RogerParkinson/vortex-manipulator/src/Sleep.cpp

/*
 * Sleep.cpp
 *
 *  Created on: 28/04/2013
 *      Author: roger
 */

#include "Sleep.h"

static uint16_t myicon[] PROGMEM = {
	0x0000,0x0000,0x0000,0x0000,0x0000,0x0000,0x0000,0x0000,0x0000,0x0000,0x0000,0x0000,0x0000,0x0000,0x0000,0x0000,0x0000,0x0000,0x0000,0x0000,0x0000,0x0000,0x0000,0x0000,0x0000,0x0000,0x0000,0x0000,
	0x0000,0x0000,0x0000,0x0000,0x0000,0x0000,0x0000,0x0000,0x0000,0x0000,0x0000,0x0000,0x0000,0x0000,0x0000,0x0000,0x0000,0x0000,0x0000,0x0000,0x0000,0x0000,0x0000,0x0000,0x0000,0x0000,0x0000,0x0000,
	0x0000,0x0000,0x0000,0x0000,0x0000,0x0000,0x0000,0x0000,0x0000,0x0000,0x0000,0x0000,0x0000,0x0000,0x0000,0x0000,0x0000,0x0000,0x0000,0x0000,0x0000,0x0000,0x0000,0x0000,0x0000,0x0000,0x0000,0x0000,
	0x0000,0x0000,0x0000,0x0000,0x0000,0x0000,0x0000,0x0000,0x0000,0x0000,0x0000,0x39c7,0x3186,0x0000,0x0000,0x0000,0x0000,0x0000,0x0000,0x0000,0x0000,0x0000,0x0000,0x0000,0x0000,0x0000,0x0000,0x0000,
	0x0000,0x0000,0x0000,0x0000,0x0000,0x0000,0x0000,0x0000,0x0000,0x630c,0xe71c,0xd69a,0x0841,0x0000,0x0000,0x0000,0x0000,0x0000,0x0000,0x0000,0x0000,0x0000,0x0000,0x0000,0x0000,0x0000,0x0000,0x0000,
	0x0000,0x0000,0x0000,0x0000,0x0000,0x0000,0x0000,0x0000,0xce59,0xffdf,0xffdf,0x0841,0x0000,0x0000,0x0000,0x0000,0x0000,0x0000,0x0000,0x0000,0x0000,0x0000,0x0000,0x0000,0x0000,0x0000,0x0000,0x0000,
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

Sleep::Sleep(): App() {
	// Keep the constructor empty and do most things in the init()
}
void Sleep::init() {
	m_icon = new Icon(28,myicon);
}

void Sleep::setup() {
	Graphics.fillScreen(BLACK);
	Graphics.setRotation(3);
	m_buttonShutdown->draw();
//	m_buttonSleep->draw();
}

void Sleep::close() {
}

boolean Sleep::touch(TS_Point p) {
	if (m_buttonShutdown->isClicked(p)) {
		m_buttonShutdown->flash();
		Hardware.shutdown();

		Appregistry.jumpToMenu();
		Appregistry.getCurrentApp()->setup();
		Appregistry.getCurrentApp()->display();
	}
	if (m_buttonSleep->isClicked(p)) {
		m_buttonSleep->flash();
		Hardware.sleep();
	}
	return true;
}
void Sleep::display() {
}

Sleep::~Sleep() {
}

App *sleep = new Sleep();
