RogerParkinson/vortex-manipulator/src/ui/Startup.h

/*
 * Startup.h
 *
 *  Created on: Oct 14, 2018
 *      Author: roger
 */

#ifndef STARTUP_H_
#define STARTUP_H_
#include "../Hardware.h"
//#define STARTUP_SLOW


class Startup {
private:
	int row;
public:
	Startup();
	virtual void run();
	virtual void print(const char *s);
	virtual void println(const char *s);
	virtual ~Startup();
};

extern Startup startup;

#endif /* STARTUP_H_ */
